MichaelStickels/Macro_Pad_2.0/KiCad/MacroPad PCB/Macro Pad 2 PCB.kicad_sch

## KiCad design KiCad/MacroPad PCB/Macro Pad 2 PCB.kicad_sch (2023-08-25)

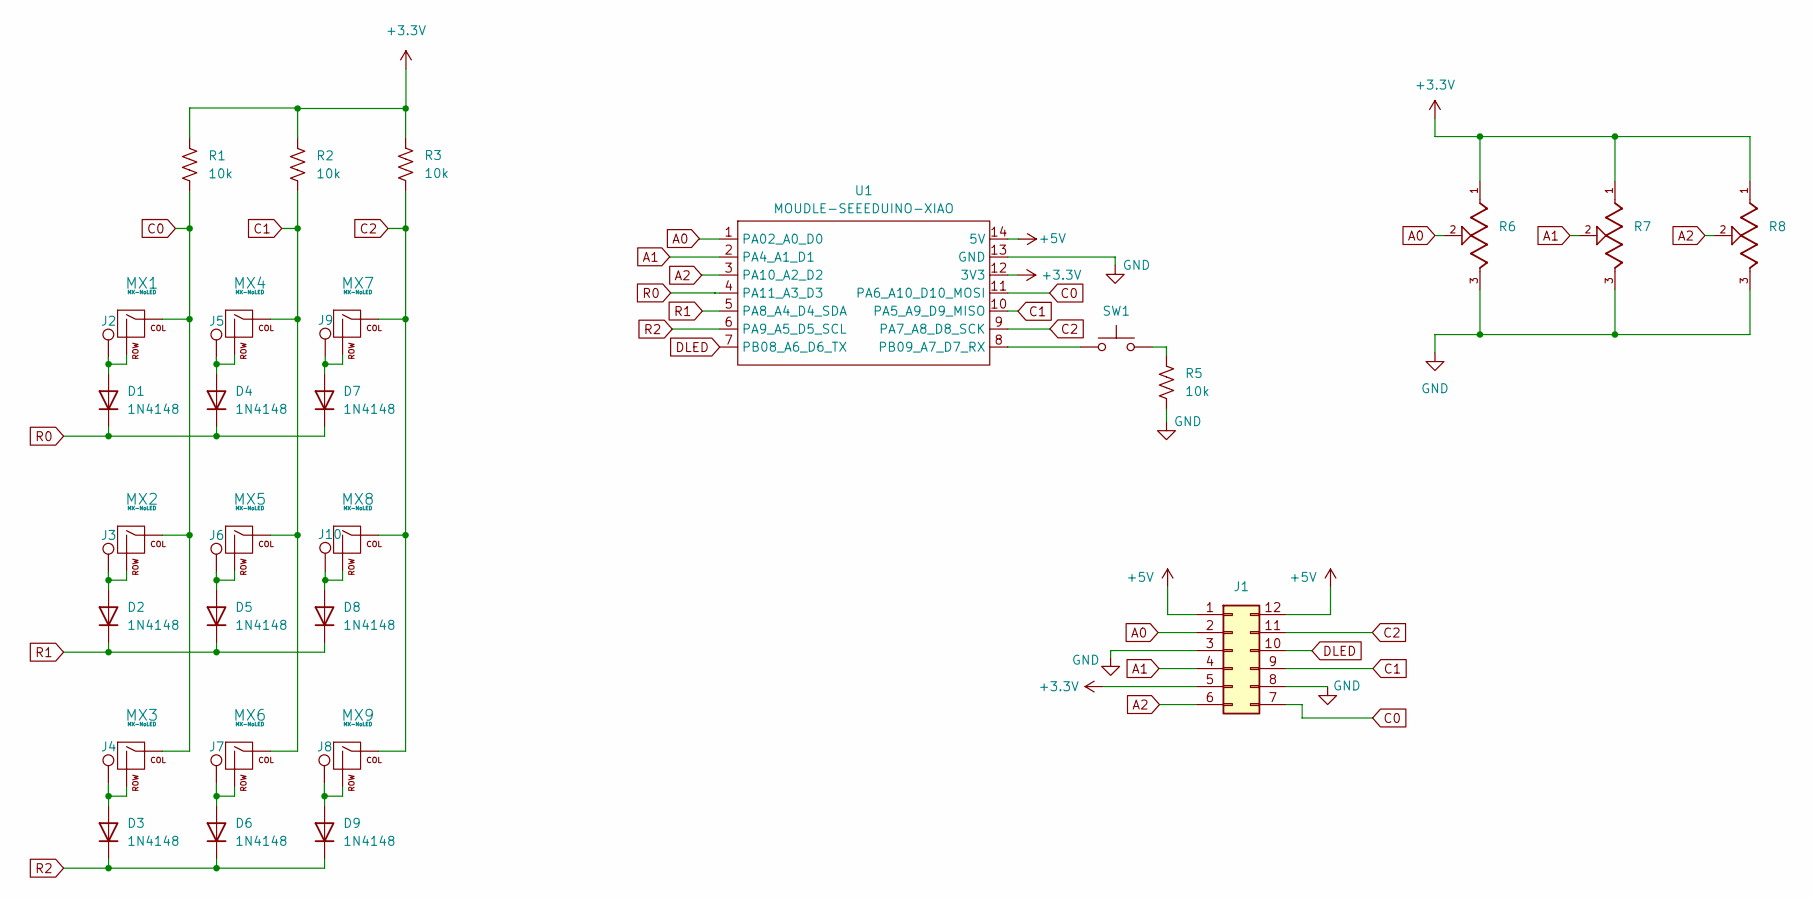
[picture p24: schematic Macro Pad 2 PCB.kicad_sch]

Parts:
D1, D2, D3, D4, D5, D6, D7, D8, D9: 1N4148; D_DO-35_SOD27_P7.62mm_Horizontal
J1: Conn_02x06_Counter_Clockwise; PinHeader_2x06_P2.54mm_Vertical_SMD
J2, J3, J4, J5, J6, J7, J8, J9, J10: TestPoint; TestPoint_Pad_2.0x2.0mm
MX1, MX2, MX3, MX4, MX5, MX6, MX7, MX8, MX9: MX-NoLED; Cherry Cutout
R1, R2, R3, R5: 10k; R_Axial_DIN0207_L6.3mm_D2.5mm_P10.16mm_Horizontal
R6, R7, R8: PTA4543-2015DPB103; Slide Pot Cutout; PARTREV 04/21
SW1: SW_MEC_5G; PushButton_6x6mm_TH_Pretty
U1: MOUDLE-SEEEDUINO-XIAO; Seeeduino XIAO-MOUDLE14P-2.54-21X17.8MM

Connections:
+3.3V: J1.5, R1.1, R2.1, R3.2, R6.1, R7.1, R8.1, U1.12 (3V3)
+5V: J1.1, J1.12, U1.14 (5V)
A0: J1.2, R6.2, U1.1 (PA02_A0_D0)
A1: J1.4, R7.2, U1.2 (PA4_A1_D1)
A2: J1.6, R8.2, U1.3 (PA10_A2_D2)
C0: J1.7, MX1.1 (COL), MX2.1 (COL), MX3.1 (COL), R1.2, U1.11 (PA6_A10_D10_MOSI)
C1: J1.9, MX4.1 (COL), MX5.1 (COL), MX6.1 (COL), R2.2, U1.10 (PA5_A9_D9_MISO)
C2: J1.11, MX7.1 (COL), MX8.1 (COL), MX9.1 (COL), R3.1, U1.9 (PA7_A8_D8_SCK)
DLED: J1.10, U1.7 (PB08_A6_D6_TX)
GND: J1.3, J1.8, R5.1, R6.3, R7.3, R8.3, U1.13 (GND)
unnamed: D1.2 (A), J2.1, MX1.2 (ROW)
unnamed: D2.2 (A), J3.1, MX2.2 (ROW)
unnamed: D3.2 (A), J4.1, MX3.2 (ROW)
unnamed: D4.2 (A), J5.1, MX4.2 (ROW)
unnamed: D5.2 (A), J6.1, MX5.2 (ROW)
unnamed: D6.2 (A), J7.1, MX6.2 (ROW)
unnamed: D7.2 (A), J9.1, MX7.2 (ROW)
unnamed: D8.2 (A), J10.1, MX8.2 (ROW)
unnamed: D9.2 (A), J8.1, MX9.2 (ROW)
unnamed: R5.2, SW1.3 (B), SW1.4 (B)
unnamed: SW1.1 (A), SW1.2 (A), U1.8 (PB09_A7_D7_RX)
R0: D1.1 (K), D4.1 (K), D7.1 (K), U1.4 (PA11_A3_D3)
R1: D2.1 (K), D5.1 (K), D8.1 (K), U1.5 (PA8_A4_D4_SDA)
R2: D3.1 (K), D6.1 (K), D9.1 (K), U1.6 (PA9_A5_D5_SCL)
